lafefspietz/muxduino/geometron/symbolfeed/symbol1726158102.png

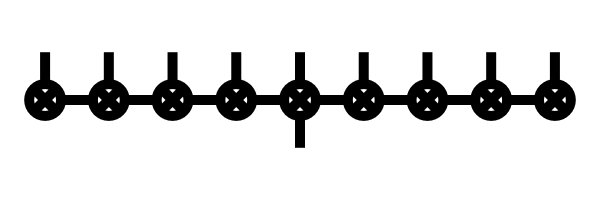
geometron/symbolfeed/symbol1726158102.png
