lafefspietz/muxduino/geometron/symbolfeed/symbol1726158213.png

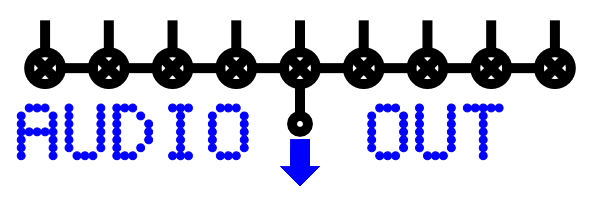
geometron/symbolfeed/symbol1726158213.png
