lafefspietz/muxduino/geometron/symbolfeed/symbol1726158546.png

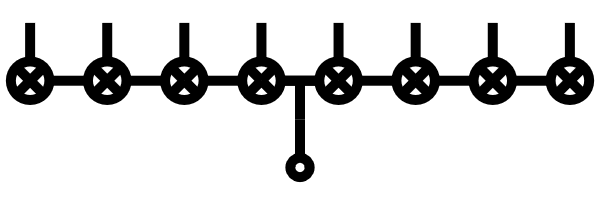
geometron/symbolfeed/symbol1726158546.png
