lafefspietz/muxduino/geometron/symbolfeed/symbol1726158583.png

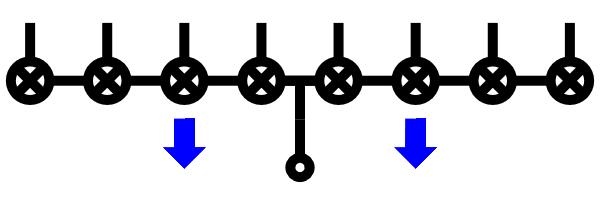
geometron/symbolfeed/symbol1726158583.png
