lafefspietz/muxduino/geometron/symbolfeed/symbol1726158624.png

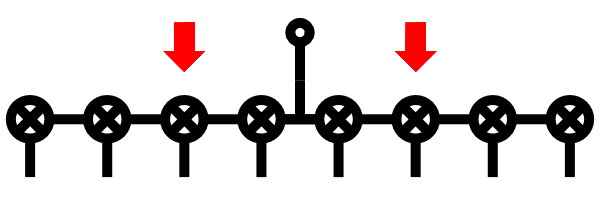
geometron/symbolfeed/symbol1726158624.png
