lafefspietz/muxduino/geometron/symbolfeed/symbol1726195868.png

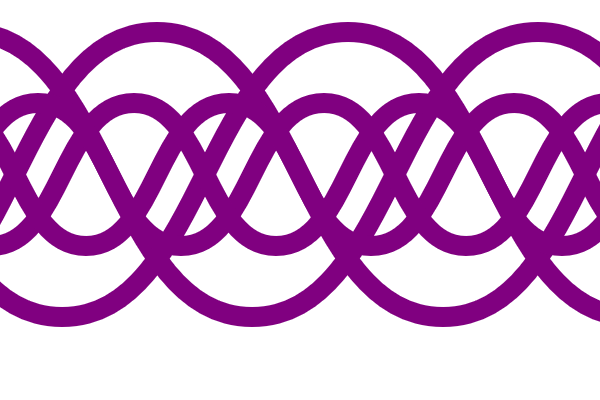
geometron/symbolfeed/symbol1726195868.png
