lafefspietz/muxduino/images/muxduino-shield-bottom.png

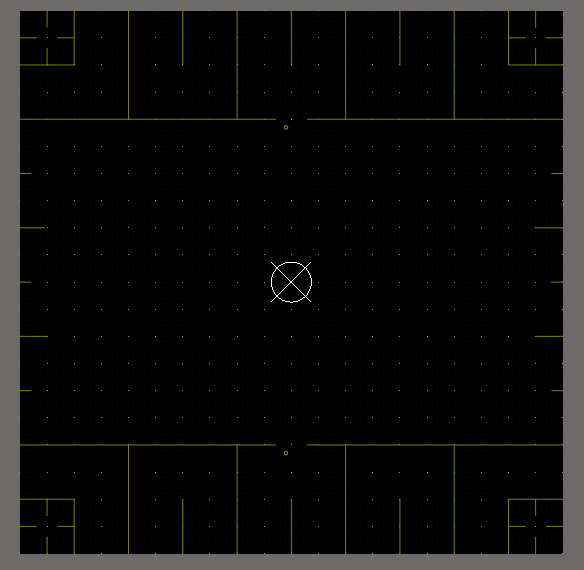
images/muxduino-shield-bottom.png
