lafefspietz/muxduino/images/muxduino-shield-silkscreen.png

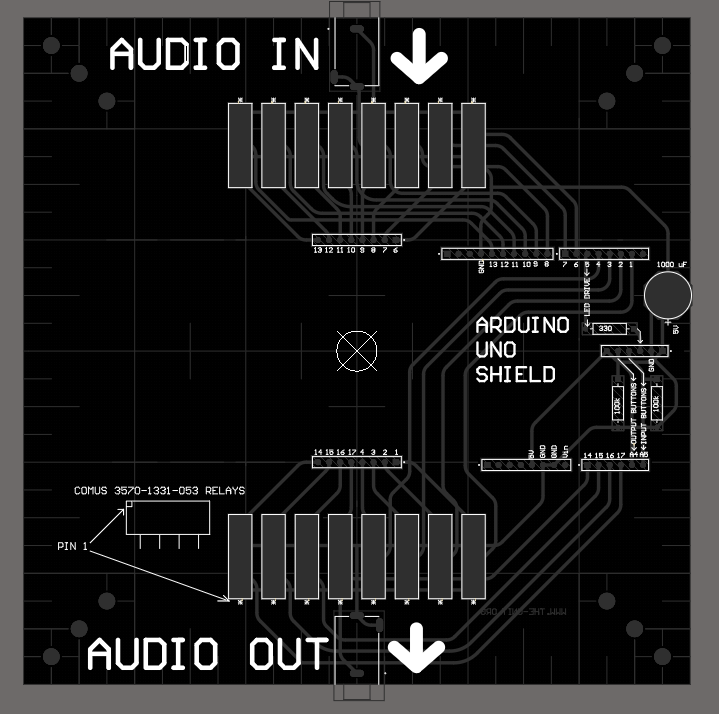
images/muxduino-shield-silkscreen.png
