lafefspietz/muxduino/images/top-board-copper.png

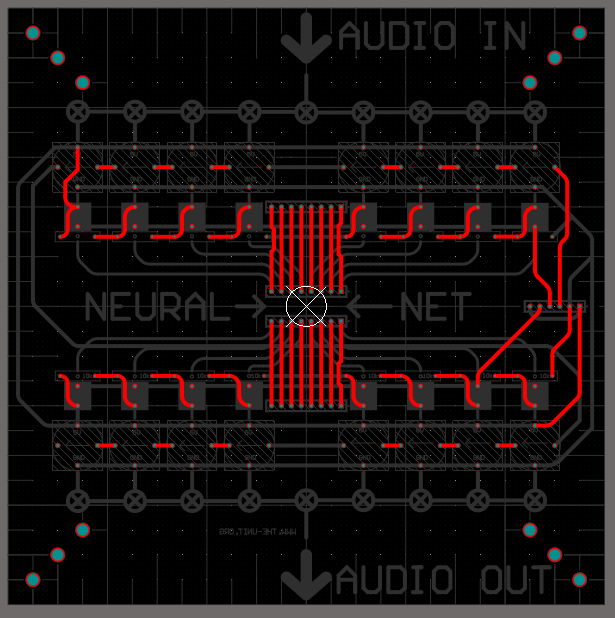
images/top-board-copper.png
