lafefspietz/muxduino/images/top-board-silkscreen-bottom.png

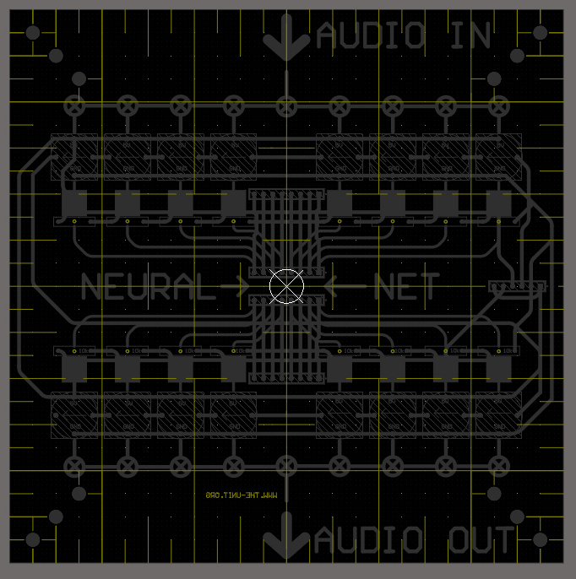
images/top-board-silkscreen-bottom.png
